jdicorpo/chipignite_discover/ChipigniteExplain.kicad_sch

## KiCad design ChipigniteExplain.kicad_sch (2025-03-31)

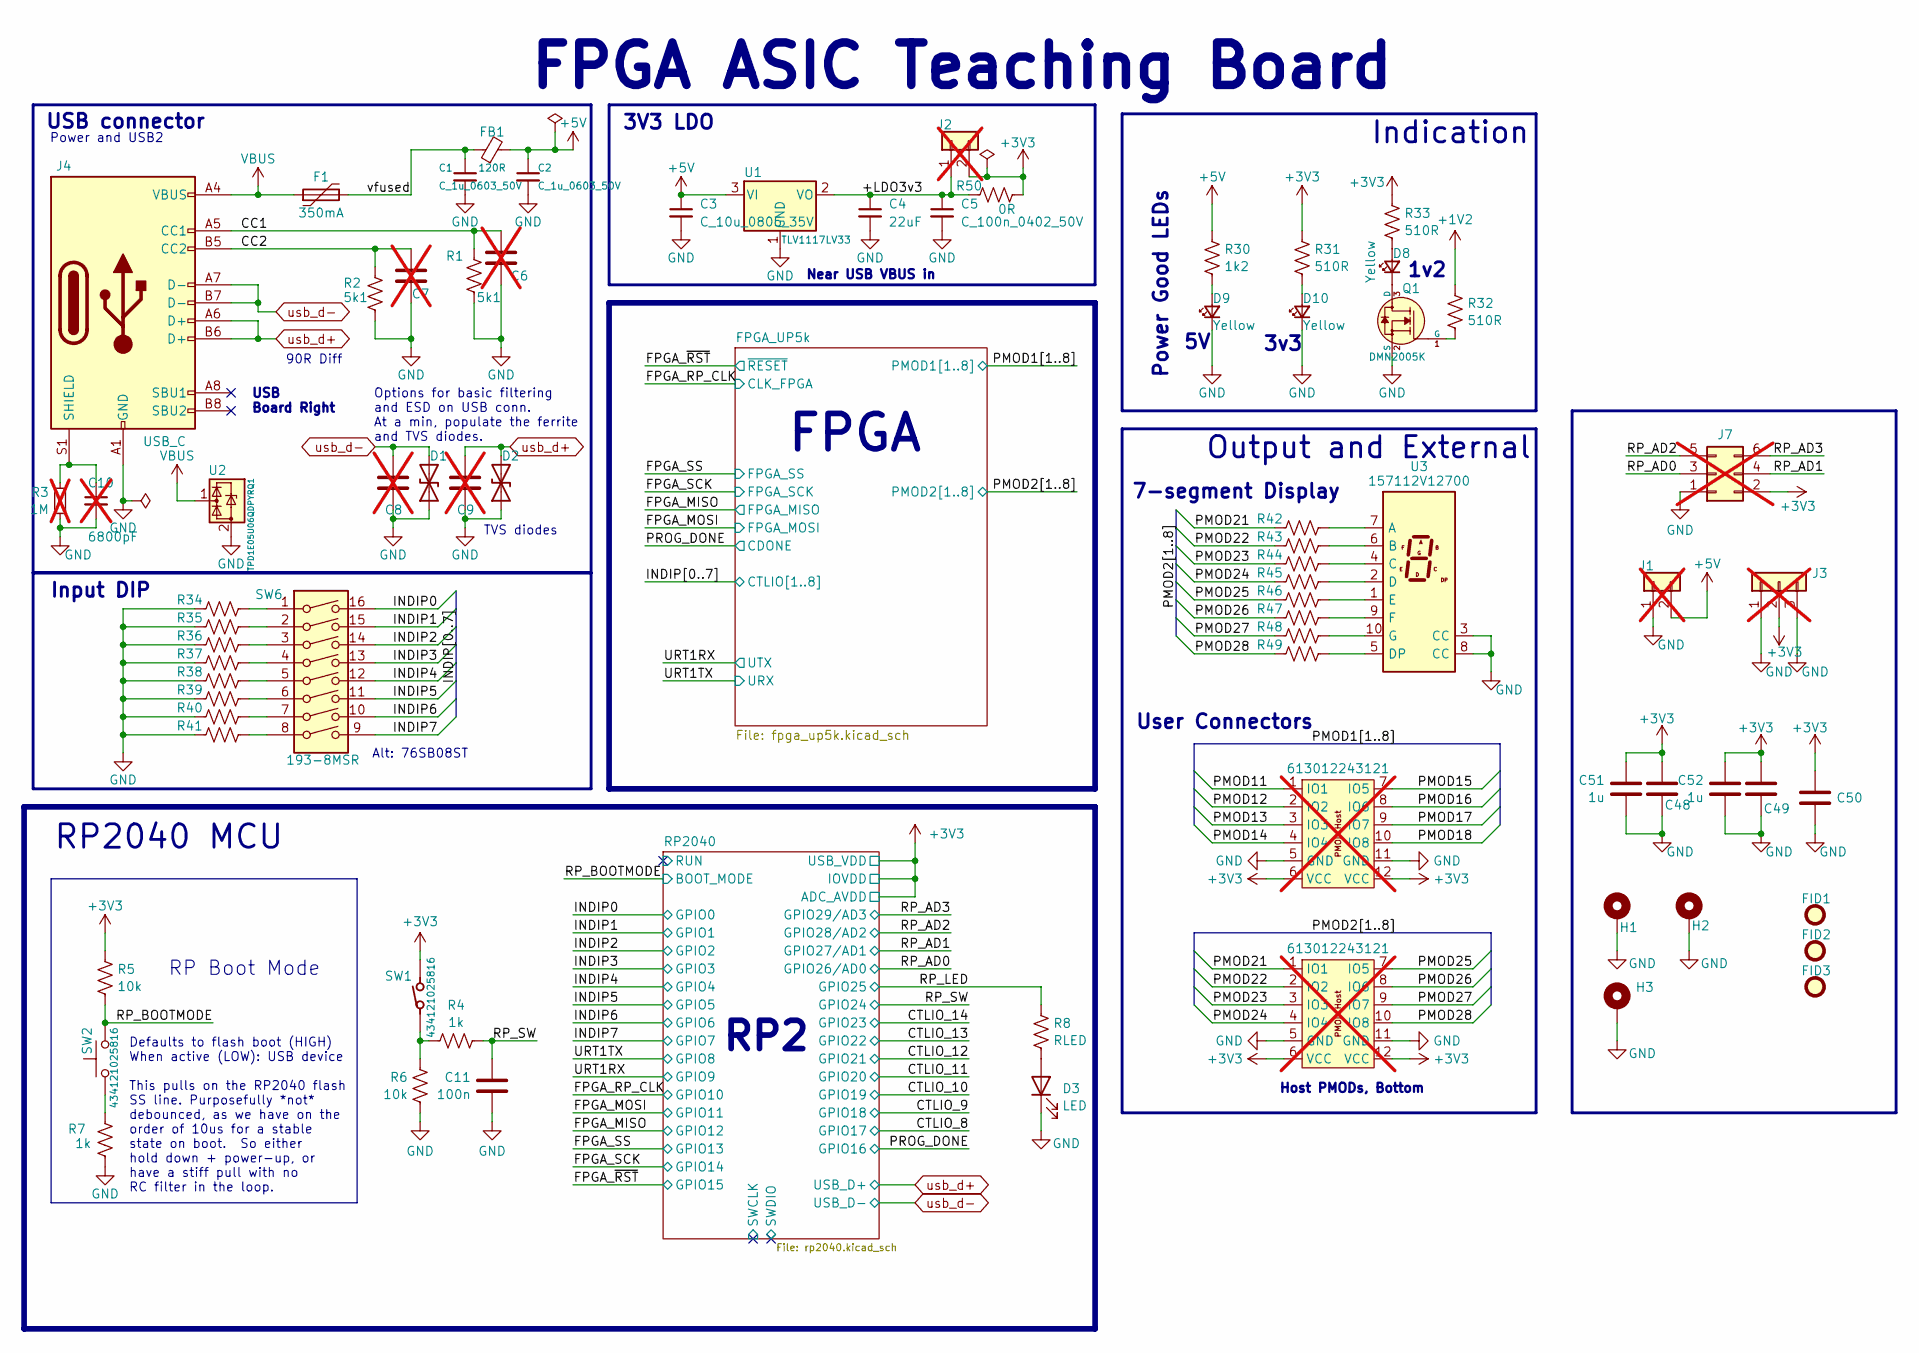
[picture p10: schematic ChipigniteExplain.kicad_sch]

Parts:
C1, C2: C_1u_0603_50V; C_0603_1608Metric; MPN CL10A105KA8NNNC; LCSC C5673
C3: C_10u_0805_35V; C_0805_2012Metric; MPN GRM21BR6YA106KE43L; LCSC C408142
C4: 22uF; C_0805_2012Metric; MPN CL21A226KOQNNNG; LCSC C86816
C5: C_100n_0402_50V; C_0402_1005Metric; MPN GRM155R71H104KE14J; LCSC C100072
C6, C7, C8, C9: C_33p_0402_50V; C_0402_1005Metric; MPN CC0402JRNPO9BN330; DigikeyPN 311-1020-1-ND; not fitted
C10: 6800pF; C_0603_1608Metric; not fitted
C11: C_100n_0402_50V; C_0402_1005Metric; MPN GRM155R71H104KE14J; DigikeyPN 490-13342-1-ND
C48, C49, C50: C_10u_0805_35V; C_0805_2012Metric; MPN GRM21BR6YA106KE43L; DigikeyPN 490-10514-1-ND
C51, C52: C_1u_0603_50V; C_0603_1608Metric; MPN CL10A105KA8NNNC; DigikeyPN 490-12330-1-ND
D1, D2: TVS; R_0603_1608Metric; MPN 0603ESDA-AEC1; DigikeyPN 283-0603ESDA-AEC1CT-ND
D3: LED; LED_0603_1608Metric
D8, D9, D10: Yellow; LED_0603_1608Metric; MPN CSL1901YW1; LCSC C72038
F1: 350mA; Fuse_0805_2012Metric; MPN 0ZCK0035FF2G; LCSC C1884490
FB1: 120R; L_0603_1608Metric; MPN MFBM1V1608-121-R; DigikeyPN 283-MFBM1V1608-121-RCT-ND
FID1, FID2, FID3: Fiducial; Fiducial_1mm_Mask2mm
H1, H2, H3: MountingHole_Pad; MountingHole_3.2mm_M3_Pad
J1: Conn_01x02; PinHeader_1x02_P2.54mm_Vertical; not fitted
J2: Conn_01x02; PinHeader_1x02_P2.54mm_Vertical_SMD_Pin1Right; MPN 10129380-902001BLF; not fitted
J3: Conn_01x03; PinHeader_1x03_P2.54mm_Vertical; not fitted
J4: USB_C; USB_C_Receptacle_HRO_TYPE-C-31-M-12; MPN USB-TYPE-C-019; DigikeyPN USB4105-GF-A-120
J5, J6: 613012243121; PinSocket_2x06_P2.54mm_PMODHost1A; not fitted
J7: Conn_02x03_Odd_Even; PinHeader_2x03_P2.54mm_Vertical; not fitted
Q1: DMN2005K; SOT-23; MPN DMN2005K-7; DigikeyPN DMN2005K-7DICT-ND
R1, R2: R_5k1_0402; R_0402_1005Metric; MPN CR0402-FX-5101GLF; DigikeyPN CR0402-FX-5101GLFCT-ND
R3: 1M; R_0603_1608Metric; LCSC C858907; not fitted
R4, R7: R_1k_0402; R_0402_1005Metric; MPN CR0402-FX-1001GLF; DigikeyPN CR0402-FX-1001GLFCT-ND
R5, R6: R_10k_0402; R_0402_1005Metric; MPN RC0402FR-0710KL; DigikeyPN 10-ERJ-U02F1002XCT-ND
R8: RLED; R_0402_1005Metric
R30: R_1k2_0402; R_0402_1005Metric; MPN RC0402FR-071K2L; DigikeyPN 311-1.20KLRCT-ND
R31, R32, R33, R34, R35, R36, R37, R38, R39, R40, R41: 510R; R_0402_1005Metric
R42, R43, R44, R45, R46, R47, R48, R49: 68R; R_0402_1005Metric
R50: R_0R_0603_JUMPER; R_0603_1608Metric; MPN CRG0603ZR; DigikeyPN A106051CT-ND
SW1: 434121025816; MPN 434121025816; DigikeyPN 2223-TS09-63-25-R-260-SMT-TRCT-ND
SW2: 434121025816; MPN 434121025816; LCSC C4364640 or C2689642 or C329185 or C268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
SW6: 193-8MSR; GENERIC_PIANO_8DIP; MPN DSPV08LSGET; LCSC C3293170
U1: TLV1117LV33; SOT-223-3_TabPin2; MPN TLV1117LV33DCYR; LCSC C15578
U2: TPD1E05U06QDPYRQ1; Texas_DPY0002A_0.6x1mm_P0.65mm; MPN TPD1E05U06QDPYRQ1; DigikeyPN 296-47863-1-ND
U3: 157112V12700; WL_S7DS-157112V12700; MPN 157112V12700; DigikeyPN 732-157112V12700DKR-ND

Connections:
+1V2: R32.1
+3V3: C48.1, C49.1, C50.1, C51.1, C52.1, J2.2, J3.2, J5.6 (VCC), J5.12 (VCC), J6.6 (VCC), J6.12 (VCC), J7.2, R5.1, R31.1, R33.1, R50.2, SW1.2
+5V: C2.1, C3.1, FB1.2, J1.2, R30.1, U1.3 (VI)
+LDO3v3: C4.1, C5.1, J2.1, R50.1, U1.2 (VO)
CC1: C6.1, J4.A5 (CC1), R1.1
CC2: C7.1, J4.B5 (CC2), R2.1
GND: C1.2, C2.2, C3.2, C4.2, C5.2, C6.2, C7.2, C8.2, C9.2, C10.2, C11.2, C48.2, C49.2, C50.2, C51.2, C52.2, D1.1 (A1), D2.1 (A1), D3.1 (K), D9.1 (K), D10.1 (K), H1.1, H2.1, H3.1, J1.1, J3.1, J3.3, J4.A1 (GND), J4.A12 (GND), J4.B1 (GND), J4.B12 (GND), J5.5 (GND), J5.11 (GND), J6.5 (GND), J6.11 (GND), J7.1, Q1.2 (S), R1.2, R2.2, R3.2, R6.2, R7.2, R34.1, R35.1, R36.1, R37.1, R38.1, R39.1, R40.1, R41.1, U1.1 (GND), U2.2 (GND), U3.3 (CC), U3.8 (CC)
INDIP0: SW6.16
INDIP1: SW6.15
INDIP2: SW6.14
INDIP3: SW6.13
INDIP4: SW6.12
INDIP5: SW6.11
INDIP6: SW6.10
INDIP7: SW6.9
unnamed: C10.1, J4.S1 (SHIELD), R3.1
unnamed: D3.2 (A), R8.2
unnamed: D8.1 (K), Q1.3 (D)
unnamed: D8.2 (A), R33.2
unnamed: D9.2 (A), R30.2
unnamed: D10.2 (A), R31.2
unnamed: Q1.1 (G), R32.2
unnamed: R4.1, R6.1, SW1.1
unnamed: R7.1, SW2.1
unnamed: R34.2, SW6.1
unnamed: R35.2, SW6.2
unnamed: R36.2, SW6.3
unnamed: R37.2, SW6.4
unnamed: R38.2, SW6.5
unnamed: R39.2, SW6.6
unnamed: R40.2, SW6.7
unnamed: R41.2, SW6.8
unnamed: R42.2, U3.7 (A)
unnamed: R43.2, U3.6 (B)
unnamed: R44.2, U3.4 (C)
unnamed: R45.2, U3.2 (D)
unnamed: R46.2, U3.1 (E)
unnamed: R47.2, U3.9 (F)
unnamed: R48.2, U3.10 (G)
unnamed: R49.2, U3.5 (DP)
PMOD11: J6.1 (IO1)
PMOD12: J6.2 (IO2)
PMOD13: J6.3 (IO3)
PMOD14: J6.4 (IO4)
PMOD15: J6.7 (IO5)
PMOD16: J6.8 (IO6)
PMOD17: J6.9 (IO7)
PMOD18: J6.10 (IO8)
PMOD21: J5.1 (IO1), R42.1
PMOD22: J5.2 (IO2), R43.1
PMOD23: J5.3 (IO3), R44.1
PMOD24: J5.4 (IO4), R45.1
PMOD25: J5.7 (IO5), R46.1
PMOD26: J5.8 (IO6), R47.1
PMOD27: J5.9 (IO7), R48.1
PMOD28: J5.10 (IO8), R49.1
RP_AD0: J7.3
RP_AD1: J7.4
RP_AD2: J7.5
RP_AD3: J7.6
RP_BOOTMODE: R5.2, SW2.2
RP_LED: R8.1
RP_SW: C11.1, R4.2
VBUS: F1.1, J4.A4 (VBUS), J4.A9 (VBUS), J4.B4 (VBUS), J4.B9 (VBUS), U2.1 (I/O)
usb_d+: C9.1, D2.2 (A2), J4.A6 (D+), J4.B6 (D+)
usb_d-: C8.1, D1.2 (A2), J4.A7 (D-), J4.B7 (D-)
vfused: C1.1, F1.2, FB1.1

Notes on the sheet:
7-segment Display
3v3
Near USB VBUS in
TVS diodes
RP Boot Mode
Output and External
Options for basic filtering and ESD on USB conn. At a min, populate the ferrite and TVS diodes.
Defaults to flash boot (HIGH) When active (LOW): USB device This pulls on the RP2040 flash SS line. Purposefully *not* debounced, as we have on the order of 10us for a stable state on boot. So either hold down + power-up, or have a stiff pull with no RC filter in the loop.
Indication
1v2
Power and USB2
3V3 LDO
USB connector
Power Good LEDs
90R Diff
Input DIP
RP2
FPGA ASIC Teaching Board
Host PMODs, Bottom
USB Board Right
Alt: 76SB08ST
User Connectors
RP2040 MCU
FPGA
