jdicorpo/chipignite_discover/fpga_up5k.kicad_sch

## KiCad design fpga_up5k.kicad_sch (2025-03-31)

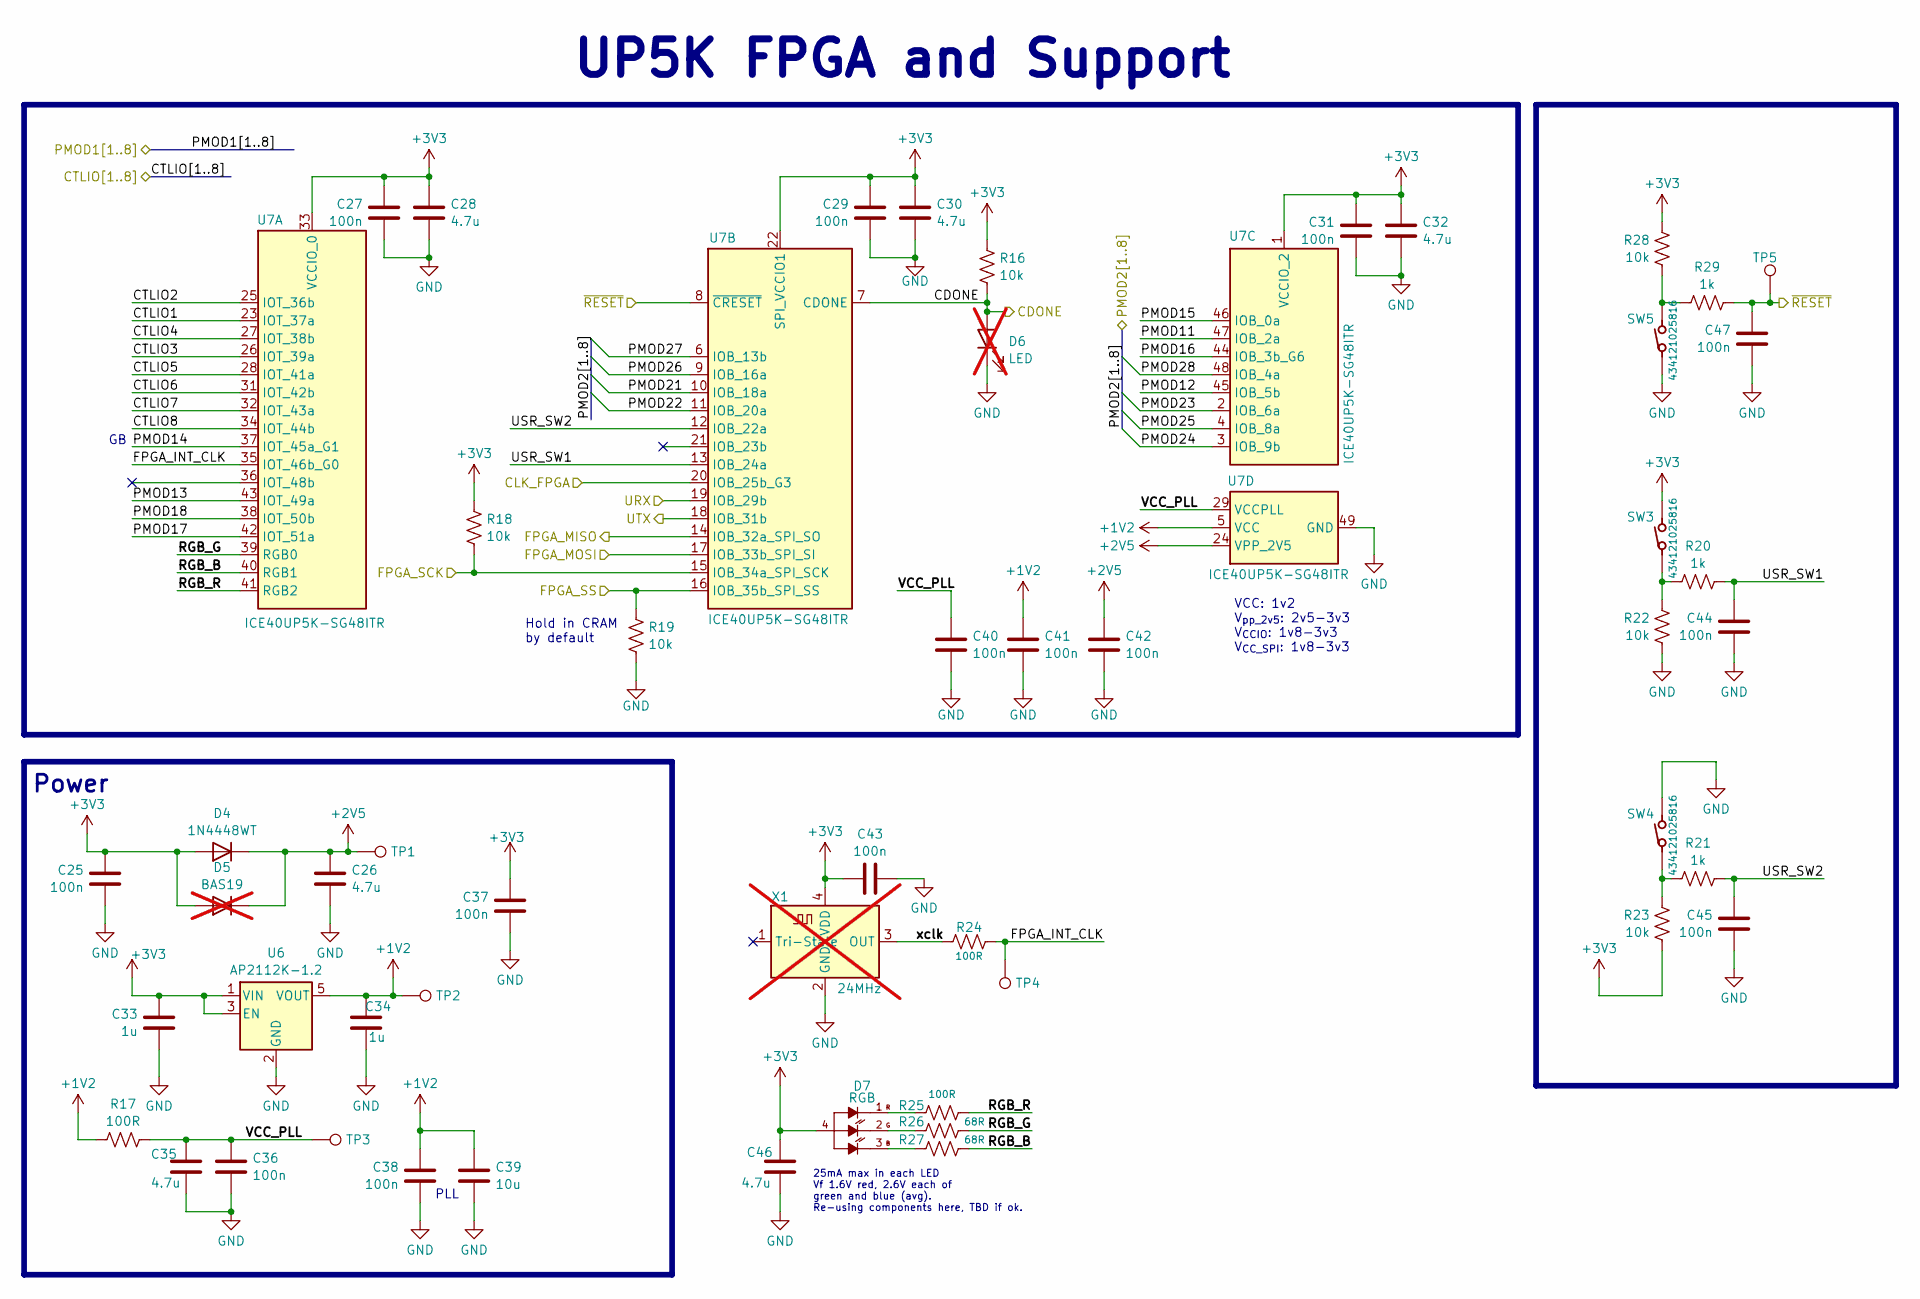
[picture p11: schematic fpga_up5k.kicad_sch]

Parts:
C25, C27, C29, C31, C36, C37, C38, C40, C41, C42, C43, C44, C45, C47: C_100n_0402_50V; C_0402_1005Metric; MPN GRM155R71H104KE14J; DigikeyPN 490-13342-1-ND
C26, C28, C30, C32, C35, C46: C_4p7u_0603_25V; C_0603_1608Metric; MPN GRM188R61E475KE11D; DigikeyPN 490-7203-1-ND
C33, C34: C_1u_0603_50V; C_0603_1608Metric; MPN CL10A105KA8NNNC; DigikeyPN 490-12330-1-ND
C39: C_10u_0603_10V; C_0603_1608Metric; MPN GRM188R61A106KE69D; DigikeyPN 490-10474-1-ND
D4: 1N4448WT; D_SOD-523; MPN 1N4448WT; DigikeyPN 1N4448WTCT-ND
D5: BAS19; SOT-23; MPN BAS19LT1G; DigikeyPN BAS19LT1GOSCT-ND; not fitted
D6: LED; LED_0603_1608Metric; not fitted
D7: RGB; LED_EAST1616RGBA3; MPN EAST1616RGBB4; DigikeyPN 1080-1552-1-ND
R16, R18, R19, R22, R23, R28: R_10k_0402; R_0402_1005Metric; MPN RC0402FR-0710KL; DigikeyPN 10-ERJ-U02F1002XCT-ND
R17, R24, R25: R_100R_0402; R_0402_1005Metric; MPN RC0402FR-07100RL; DigikeyPN 311-100LRCT-ND
R20, R21, R29: R_1k_0402; R_0402_1005Metric; MPN CR0402-FX-1001GLF; DigikeyPN CR0402-FX-1001GLFCT-ND
R26, R27: R_68R_0402; R_0402_1005Metric; MPN CR0402-FX-68R0GLF; DigikeyPN CR0402-FX-68R0GLFCT-ND
SW3, SW4, SW5: 434121025816; MPN 434121025816; DigikeyPN 2223-TS09-63-25-R-260-SMT-TRCT-ND
TP1, TP2, TP3, TP4, TP5: TestPoint; TestPoint_Pad_D1.5mm
U6: AP2112K-1.2; SOT-23-5; MPN AP2112K-1.2TRG1; DigikeyPN 31-AP2112K-1.2TRG1CT-ND
U7: ICE40UP5K-SG48ITR; QFN-48-1EP_7x7mm_P0.5mm_EP5.6x5.6mm; MPN ICE40UP5K-SG48ITR
X1: 24MHz; Oscillator_SMD_ECS_2520MV-xxx-xx-4Pin_2.5x2.0mm; MPN KC2520Z24.0000C1KX00; DigikeyPN 478-KC2520Z24.0000C1KX00DKR-ND; not fitted

Connections:
+1V2: C34.1, C38.1, C39.1, C41.1, R17.1, TP2.1, U6.5 (VOUT), U7.5 (VCC), U7.30 (VCC)
+2V5: C26.1, C42.1, D4.1 (K), D5.3 (K), TP1.1, U7.24 (VPP_2V5)
+3V3: C25.1, C27.1, C28.1, C29.1, C30.1, C31.1, C32.1, C33.1, C37.1, C43.1, C46.1, D4.2 (A), D5.1 (A), D7.4, R16.1, R18.1, R23.2, R28.1, SW3.2, U6.1 (VIN), U6.3 (EN), U7.1 (VCCIO_2), U7.22 (SPI_VCCIO1), U7.33 (VCCIO_0), X1.4 (VDD)
CDONE: D6.2 (A), R16.2, U7.7 (CDONE)
CLK_FPGA: U7.20 (IOB_25b_G3)
CTLIO1: U7.23 (IOT_37a)
CTLIO2: U7.25 (IOT_36b)
CTLIO3: U7.26 (IOT_39a)
CTLIO4: U7.27 (IOT_38b)
CTLIO5: U7.28 (IOT_41a)
CTLIO6: U7.31 (IOT_42b)
CTLIO7: U7.32 (IOT_43a)
CTLIO8: U7.34 (IOT_44b)
FPGA_INT_CLK: R24.2, TP4.1, U7.35 (IOT_46b_G0)
FPGA_MISO: U7.14 (IOB_32a_SPI_SO)
FPGA_MOSI: U7.17 (IOB_33b_SPI_SI)
FPGA_SCK: R18.2, U7.15 (IOB_34a_SPI_SCK)
FPGA_SS: R19.1, U7.16 (IOB_35b_SPI_SS)
GND: C25.2, C26.2, C27.2, C28.2, C29.2, C30.2, C31.2, C32.2, C33.2, C34.2, C35.2, C36.2, C37.2, C38.2, C39.2, C40.2, C41.2, C42.2, C43.2, C44.2, C45.2, C46.2, C47.2, D6.1 (K), R19.2, R22.2, SW4.2, SW5.1, U6.2 (GND), U7.49 (GND), X1.2 (GND)
unnamed: D7.1, R25.1
unnamed: D7.2, R26.1
unnamed: D7.3, R27.1
unnamed: R20.1, R22.1, SW3.1
unnamed: R21.1, R23.1, SW4.1
unnamed: R28.2, R29.1, SW5.2
PMOD11: U7.47 (IOB_2a)
PMOD12: U7.45 (IOB_5b)
PMOD13: U7.43 (IOT_49a)
PMOD14: U7.37 (IOT_45a_G1)
PMOD15: U7.46 (IOB_0a)
PMOD16: U7.44 (IOB_3b_G6)
PMOD17: U7.42 (IOT_51a)
PMOD18: U7.38 (IOT_50b)
PMOD21: U7.10 (IOB_18a)
PMOD22: U7.11 (IOB_20a)
PMOD23: U7.2 (IOB_6a)
PMOD24: U7.3 (IOB_9b)
PMOD25: U7.4 (IOB_8a)
PMOD26: U7.9 (IOB_16a)
PMOD27: U7.6 (IOB_13b)
PMOD28: U7.48 (IOB_4a)
RGB_B: R27.2, U7.40 (RGB1)
RGB_G: R26.2, U7.39 (RGB0)
RGB_R: R25.2, U7.41 (RGB2)
URX: U7.19 (IOB_29b)
USR_SW1: C44.1, R20.2, U7.13 (IOB_24a)
USR_SW2: C45.1, R21.2, U7.12 (IOB_22a)
UTX: U7.18 (IOB_31b)
VCC_PLL: C35.1, C36.1, C40.1, R17.2, TP3.1, U7.29 (VCCPLL)
xclk: R24.1, X1.3 (OUT)
~RESET: C47.1, R29.2, TP5.1, U7.8 (~CRESET)

Notes on the sheet:
UP5K FPGA and Support
PLL
Hold in CRAM by default
25mA max in each LED Vf 1.6V red, 2.6V each of green and blue (avg). Re-using components here, TBD if ok.
Power
VCC: 1v2 V_{pp_2v5}: 2v5-3v3 V_{CCIO}: 1v8-3v3 V_{CC_SPI}: 1v8-3v3
