jdicorpo/chipignite_discover/rp2040.kicad_sch

## KiCad design rp2040.kicad_sch (2025-03-31)

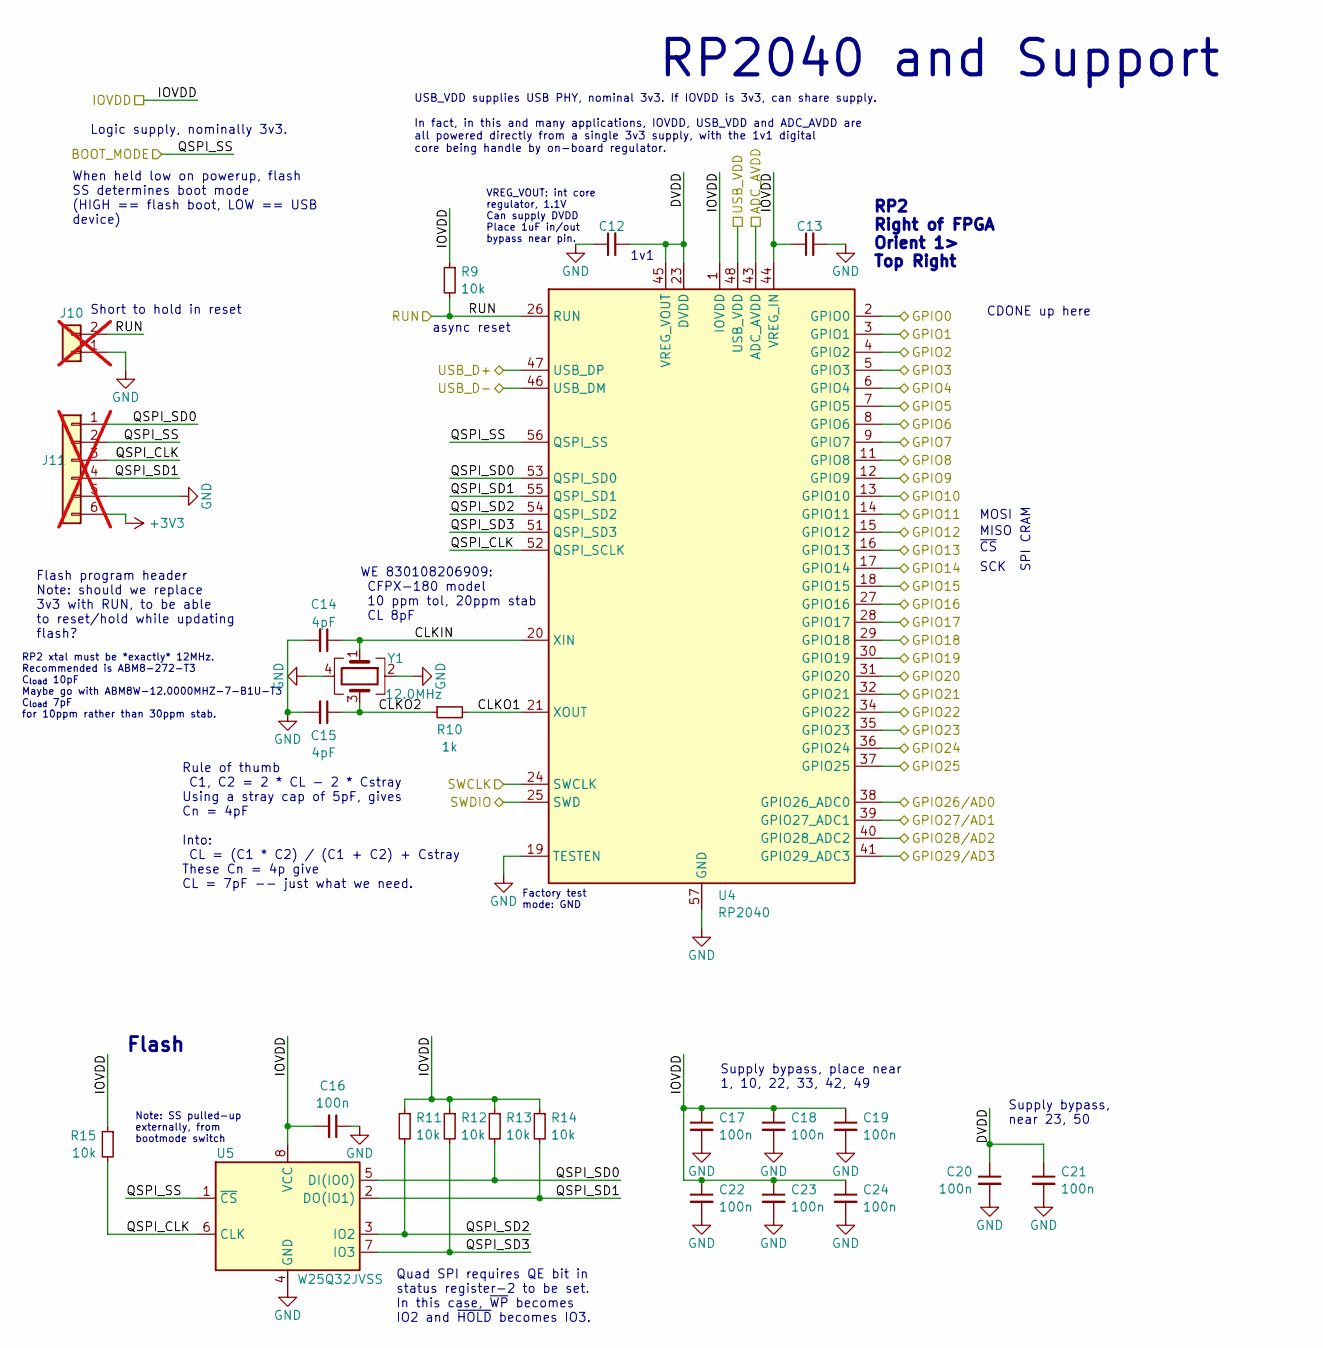
[picture p12: schematic rp2040.kicad_sch]

Parts:
C12, C13: C_1u_0603_50V; C_0603_1608Metric; MPN CL10A105KA8NNNC; LCSC C5673
C14, C15: 4pF; C_0402_1005Metric; MPN CC0402CRNPO9BN4R0; LCSC C325455
C16, C17, C18, C19, C20, C21, C22, C23, C24: C_100n_0402_50V; C_0402_1005Metric; MPN GRM155R71H104KE14J; LCSC C100072
J10: Conn_01x02; PinHeader_1x02_P2.54mm_Vertical; not fitted
J11: Conn_01x06; PinHeader_1x06_P2.54mm_Vertical_SMD_Pin1Right; MPN 61300611121; not fitted
R9, R11, R12, R13, R14, R15: R_10k_0402; R_0402_1005Metric; MPN RC0402FR-0710KL; LCSC C471764
R10: R_1k_0402; R_0402_1005Metric; MPN CR0402-FX-1001GLF; LCSC C202394
U4: RP2040; QFN-56-1EP_7x7mm_P0.4mm_EP3.2x3.2mm; MPN SC0914(13); DigikeyPN 2648-SC0914(13)CT-ND
U5: W25Q32JVSS; SOIC-8_5.23x5.23mm_P1.27mm; MPN W25Q32JVSSIQ; DigikeyPN W25Q32JVSSIQ-ND
Y1: 12.0MHz; Crystal_SMD_3225-4Pin_3.2x2.5mm; MPN ABM8W-12.0000MHZ-7-B1U-T3; DigikeyPN 535-14005-1-ND

Connections:
+3V3: J11.6
ADC_AVDD: U4.43 (ADC_AVDD)
BOOT_MODE: J11.2, U4.56 (QSPI_SS), U5.1 (~CS)
CLKIN: C14.1, U4.20 (XIN), Y1.1
CLKO1: R10.2, U4.21 (XOUT)
CLKO2: C15.1, R10.1, Y1.3
DVDD: C12.2, C20.1, C21.1, U4.23 (DVDD), U4.45 (VREG_VOUT), U4.50 (DVDD)
GND: C12.1, C13.2, C14.2, C15.2, C16.1, C17.2, C18.2, C19.2, C20.2, C21.2, C22.2, C23.2, C24.2, J10.1, J11.5, U4.19 (TESTEN), U4.57 (GND), U5.4 (GND), Y1.2, Y1.4
GPIO0: U4.2 (GPIO0)
GPIO1: U4.3 (GPIO1)
GPIO2: U4.4 (GPIO2)
GPIO3: U4.5 (GPIO3)
GPIO4: U4.6 (GPIO4)
GPIO5: U4.7 (GPIO5)
GPIO6: U4.8 (GPIO6)
GPIO7: U4.9 (GPIO7)
GPIO8: U4.11 (GPIO8)
GPIO9: U4.12 (GPIO9)
GPIO10: U4.13 (GPIO10)
GPIO11: U4.14 (GPIO11)
GPIO12: U4.15 (GPIO12)
GPIO13: U4.16 (GPIO13)
GPIO14: U4.17 (GPIO14)
GPIO15: U4.18 (GPIO15)
GPIO16: U4.27 (GPIO16)
GPIO17: U4.28 (GPIO17)
GPIO18: U4.29 (GPIO18)
GPIO19: U4.30 (GPIO19)
GPIO20: U4.31 (GPIO20)
GPIO21: U4.32 (GPIO21)
GPIO22: U4.34 (GPIO22)
GPIO23: U4.35 (GPIO23)
GPIO24: U4.36 (GPIO24)
GPIO25: U4.37 (GPIO25)
GPIO26/AD0: U4.38 (GPIO26_ADC0)
GPIO27/AD1: U4.39 (GPIO27_ADC1)
GPIO28/AD2: U4.40 (GPIO28_ADC2)
GPIO29/AD3: U4.41 (GPIO29_ADC3)
IOVDD: C13.1, C16.2, C17.1, C18.1, C19.1, C22.1, C23.1, C24.1, R9.1, R11.1, R12.1, R13.1, R14.1, R15.1, U4.1 (IOVDD), U4.10 (IOVDD), U4.22 (IOVDD), U4.33 (IOVDD), U4.42 (IOVDD), U4.44 (VREG_IN), U4.49 (IOVDD), U5.8 (VCC)
QSPI_CLK: J11.3, R15.2, U4.52 (QSPI_SCLK), U5.6 (CLK)
QSPI_SD0: J11.1, R13.2, U4.53 (QSPI_SD0), U5.5 (DI(IO0))
QSPI_SD1: J11.4, R14.2, U4.55 (QSPI_SD1), U5.2 (DO(IO1))
QSPI_SD2: R11.2, U4.54 (QSPI_SD2), U5.3 (IO2)
QSPI_SD3: R12.2, U4.51 (QSPI_SD3), U5.7 (IO3)
RUN: J10.2, R9.2, U4.26 (RUN)
SWCLK: U4.24 (SWCLK)
SWDIO: U4.25 (SWD)
USB_D+: U4.47 (USB_DP)
USB_D-: U4.46 (USB_DM)
USB_VDD: U4.48 (USB_VDD)

Notes on the sheet:
CDONE up here
async reset
RP2040 and Support
Flash
Short to hold in reset
VREG_VOUT: int core regulator, 1.1V Can supply DVDD Place 1uF in/out bypass near pin.
When held low on powerup, flash SS determines boot mode (HIGH == flash boot, LOW == USB device)
WE 830108206909: CFPX-180 model 10 ppm tol, 20ppm stab CL 8pF
1v1
RP2 Right of FPGA Orient 1> Top Right
USB_VDD supplies USB PHY, nominal 3v3. If IOVDD is 3v3, can share supply. In fact, in this and many applications, IOVDD, USB_VDD and ADC_AVDD are all powered directly from a single 3v3 supply, with the 1v1 digital core being handle by on-board regulator.
Flash program header Note: should we replace 3v3 with RUN, to be able to reset/hold while updating flash?
Supply bypass, place near 1, 10, 22, 33, 42, 49
Quad SPI requires QE bit in status register-2 to be set. In this case, ~{WP} becomes IO2 and ~{HOLD} becomes IO3.
Factory test mode: GND
Rule of thumb C1, C2 = 2 * CL - 2 * Cstray Using a stray cap of 5pF, gives Cn = 4pF Into: CL = (C1 * C2) / (C1 + C2) + Cstray These Cn = 4p give CL = 7pF -- just what we need.
~{CS}
Logic supply, nominally 3v3.
RP2 xtal must be *exactly* 12MHz. Recommended is ABM8-272-T3 C_{load} 10pF Maybe go with ABM8W-12.0000MHZ-7-B1U-T3 C_{load} 7pF for 10ppm rather than 30ppm stab.
SCK
SPI CRAM
Supply bypass, near 23, 50
MOSI
Note: SS pulled-up externally, from bootmode switch
MISO
